franziskusehmeir/SliDIY_OG/asciidocs/images/deployment_diagram.PNG

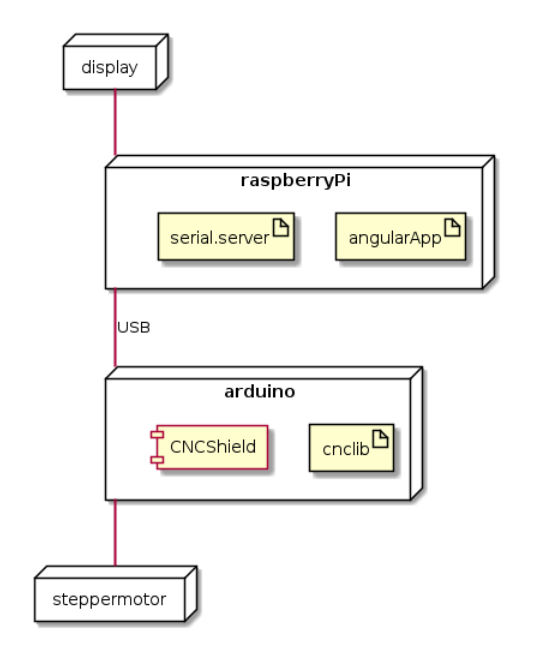
asciidocs/images/deployment_diagram.PNG
