franziskusehmeir/SliDIY_OG/asciidocs/images/ucd.PNG

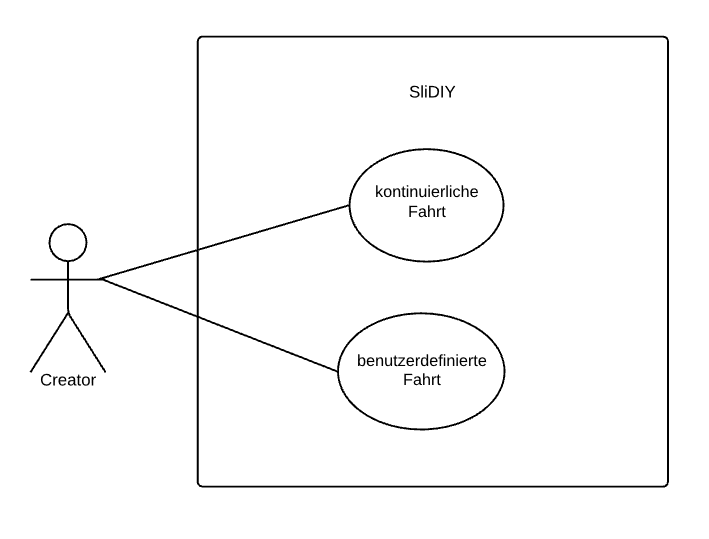
asciidocs/images/ucd.PNG
