franziskusehmeir/SliDIY_OG/docs/images/team.png

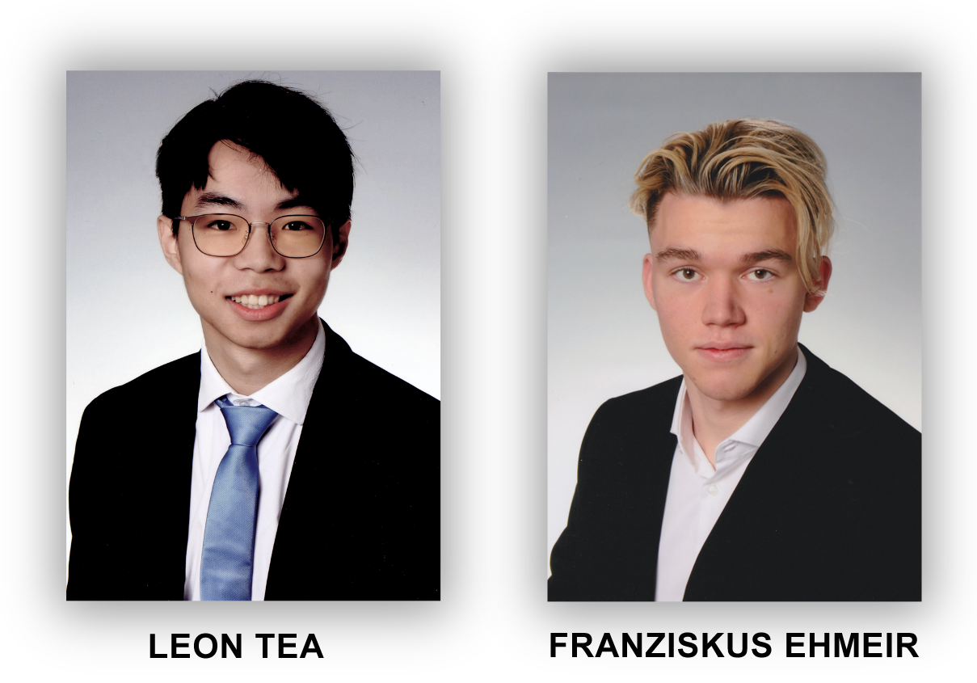
docs/images/team.png
